jonsowman/evlogger/src/system.c

/**
 * Handles intrinsic system functionality such as controlling the CPU core
 * clock and ensuring its stability, providing a real time "wall clock" source,
 * etc.
 *
 * The core clock is generated using onboard equipment, with the reference
 * being an external 4MHz high precision crystal. Since the core clock
 * frequency is much higher than the reference, a frequency locked loop (FLL)
 * system is paired with a digitally controlled oscillator (DCO) to provide a
 * stabilised source via feedback. This system is fantastically complicated and
 * reading of the datasheet (specific to the F5529) is recommended before
 * attempting to understand what is going on in this module!
 *
 * @file system.c
 * @author Jon Sowman, University of Southampton <j.sowman@soton.ac.uk>
 * @copyright Jon Sowman 2014, All Rights Reserved
 * @addtogroup System
 * @{
 */

#include <in430.h>
#include "HAL_PMM.h"
#include "system.h"

/** Current clock time */
static volatile clock_time_t ticks;

/**
 * Use timer A0 to set up a system clock ticking at 1ms intervals.
 */
void clock_init(void)
{
    // Reset the local tick counter and set function ptrs to null
    ticks = 0;

    // Count to 24999 (25000 actual counts)
    TA0CCR0 = 24999;

    // Clock from SMCLK with no divider, use "up" mode, use interrupts
    TA0CTL |= TASSEL_2 | MC_1 | TACLR;

    // CCR0 interrupt enable
    TA0CCTL0 |= CCIE;

    // Enable global interrupts (macro from legacymsp430.h) and return
    eint();
    return;
}

/**
 * Configure the system core clock to provide a stable clock for the CPU.
 *
 * Set up the system core clock source as the digitally controlled 
 * oscillator (DCO) and have the FLL stabilise the DCO at 25MHz with reference
 * to the external high speed crystal XT2, which is 4MHz on the MSP-EXP430
 * board.
 */
void sys_clock_init(void)
{
    uint16_t i;

    SetVCore(3);

    // Port select XT2
    P5SEL |= (1 << 2) | (1 << 3);

    // Setting SCG0 disables the FLL on the F5529
    __bis_status_register(SCG0);

    // Enable XT2 (4MHz xtal attached to XT2) and disable XT1 (LF & HF)
    UCSCTL6 &= ~XT2OFF;
    UCSCTL6 |= XT1OFF;
    _BIS_SR(OSCOFF); // Disable LFXT1

    // Wait for XT2 to stabilise
    do {
        UCSCTL7 &= ~XT2OFFG;
        for( i = 0xFFF; i > 0; i--);
    } while( UCSCTL7 & XT2OFFG );

    // Set DCO to lowest tap
    UCSCTL0 = 0x0000;

    // Set FLL reference to be XT2 divided by 4 (FLLREFDIV=4). XT2 is a 4MHz
    // crystal, so FLLREFCLK is now 1MHz
    UCSCTL3 = SELREF__XT2CLK | FLLREFDIV__4;

    // Set the FLL loop divider to 1 (FLLD=1) and the multiplier to 25 (N=24)
    // DCOCLK = D * (N+1) * (FLLREFCLK / FLLREFDIV)
    UCSCTL2 &= ~(0x03FF);
    UCSCTL2 = 24;
    UCSCTL2 |= FLLD__1; // compensate for N=0 disallowed

    // Set the DCO to range 6 (10.7 - 39.0MHz, target 25MHz)
    // NB: f_dco_max(n, 0) < f_target < f_dco_min(n, 31)
    // See footnote, p.61, F5529 specific datasheet
    UCSCTL1 = DCORSEL_6;

    // Re-enable the FLL and wait until the DCO stabilises
    __bic_status_register(SCG0);
    do {
        UCSCTL7 &= ~DCOFFG;
        for( i = 0xFFF; i > 0; i--);
    } while( UCSCTL7 & DCOFFG );

    // At this point, DCOCLK is a 25MHz stabilised reference
    // So set MCLK and SMCLK to use this
    UCSCTL4 = SELS_3 | SELM_3;
}

/**
 * Return the current system time.
 * @returns The current clock time in milliseconds.
 */
clock_time_t clock_time(void)
{
    return ticks;
}

/**
 * Delay for the provided number of milliseconds. We use the __delay_cycles()
 * function which consists of putting NOPs into the CPU pipeline for the
 * required period.
 * @param delay The number of ms to delay.
 */ 
void _delay_ms(clock_time_t delay)
{
    clock_time_t i;
    for(i=0; i < delay; i++)
    {
        __delay_cycles(25000);
    }
}

/**
 * Interrupt service routine for the system ticks counter.
 * Note that the interrupt() macro is from legacymsp430.h.
 */
interrupt(TIMER0_A0_VECTOR) TIMER0_A0_ISR(void)
{
    ticks++;
}

/**
 * @}
 */
