jonsowman/evlogger/clock.c

/**
 * EV Datalogger Project
 *
 * Jon Sowman 2013 <js39g13@soton.ac.uk>
 * University of Southampton
 */

#include "clock.h"

volatile uint32_t ticks;

// We can register a function to be called at each of 10ms, 100ms, and 1s
void (*fn_10ms)(void);
void (*fn_100ms)(void);
void (*fn_1s)(void);

/**
 * Use timer A0 to set up a system clock ticking at 1ms intervals.
 * We will register functions to be called at 1ms, 10ms and 100ms intervals.
 */
void clock_init(void)
{
    // Reset the local tick counter and set function ptrs to null
    ticks = 0;
    fn_10ms = fn_100ms = fn_1s = NULL;

    // Count to 19999 (20000 actual counts)
    TA0CCR0 = 19999;

    // Clock from SMCLK with no divider, use "up" mode, use interrupts
    TA0CTL |= TASSEL_2 | MC_1 | TACLR;

    // CCR0 interrupt enable
    TA0CCTL0 |= CCIE;

    // Enable global interrupts (macro from legacymsp430.h) and return
    eint();
    return;
}

/**
 * Return the current system time
 */
uint32_t clock_time(void)
{
    return ticks;
}

/**
 * Register a function to be run by the clock module every
 * ten milliseconds (10ms)
 * \param function_10ms The pointer to the function to be run
 */
void register_function_10ms(void (*function_10ms)(void))
{
    fn_10ms = function_10ms;
}

/**
 * Register a function to be run by the clock module every
 * one hundred milliseconds (100ms)
 * \param function_100ms The pointer to the function to be run
 */
void register_function_100ms(void (*function_100ms)(void))
{
    fn_100ms = function_100ms;
}

/**
 * Register a function to be run by the clock module every 
 * one second period.
 * \param function_1s The pointer to the function to be run
 */
void register_function_1s(void (*function_1s)(void))
{
    fn_1s = function_1s;
}

/**
 * Interrupt service routine for the system ticks counter.
 * the interrupt() macro is from legacymsp430.h
 */
interrupt(TIMER0_A0_VECTOR) TIMER0_A0_ISR(void)
{
    ticks++;

    // Run through and call all registered functions
    if(ticks % 10 == 0)
        if(fn_10ms != NULL) (*fn_10ms)();

    if(ticks % 100 == 0)
        if(fn_100ms != NULL) (*fn_100ms)();

    if(ticks % 1000 == 0)
        if(fn_1s != NULL) (*fn_1s)();
}
